joeskolengaden/marwin/Gallery/3.jpg

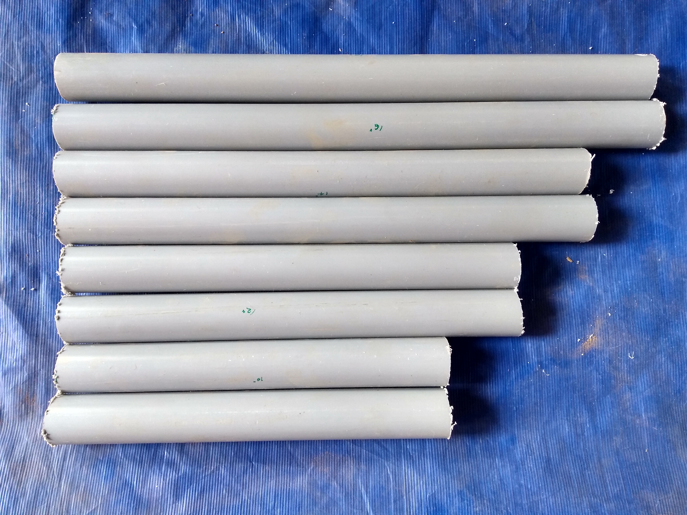
Gallery/3.jpg
