joeskolengaden/marwin/Gallery/4.jpg

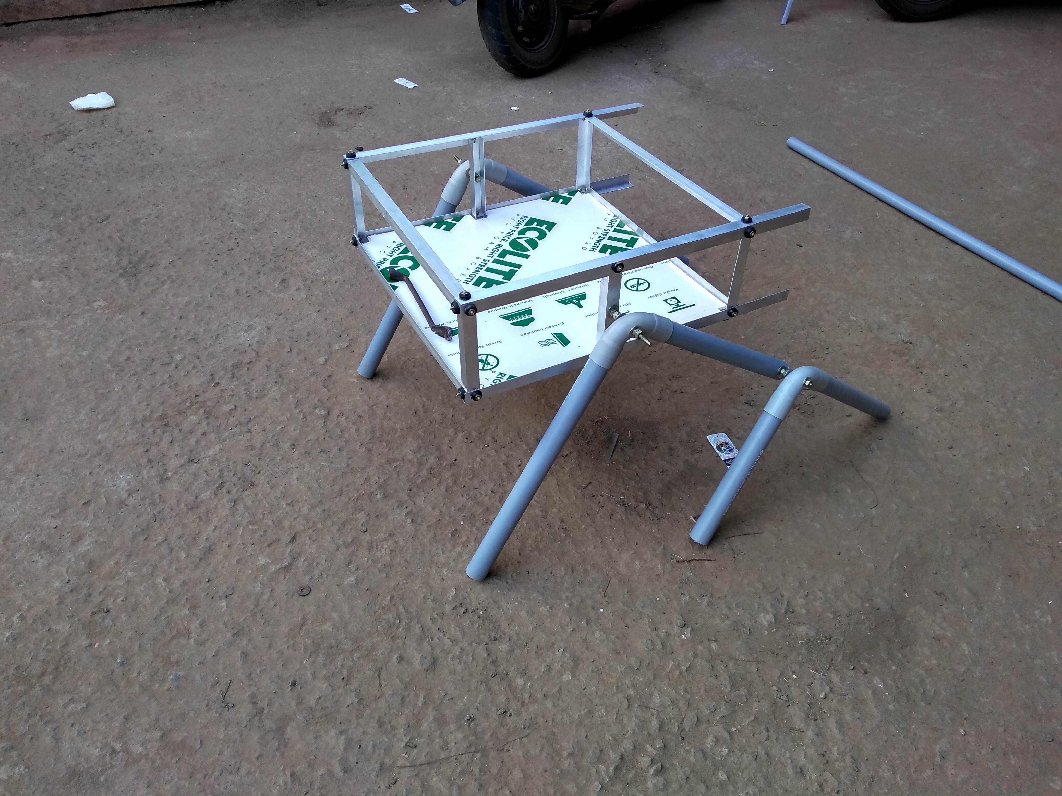
Gallery/4.jpg
