joeskolengaden/marwin/Gallery/5.jpg

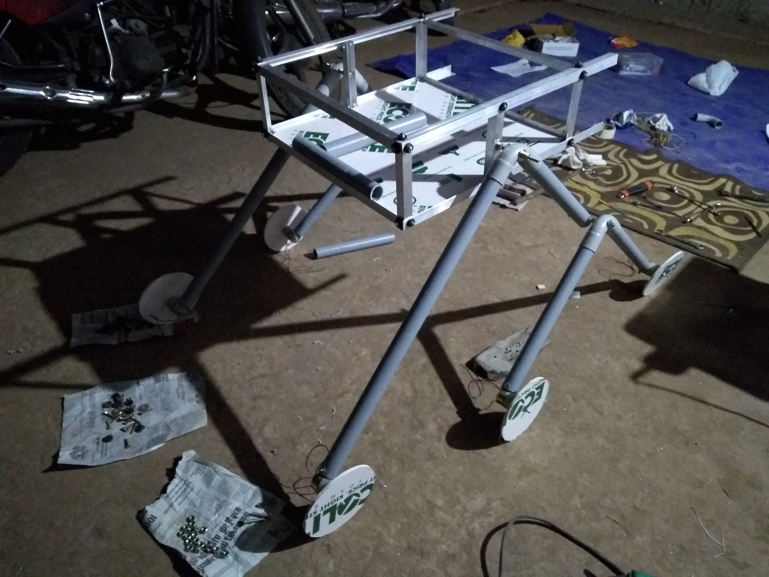
Gallery/5.jpg
