joeskolengaden/marwin/Gallery/6.jpeg

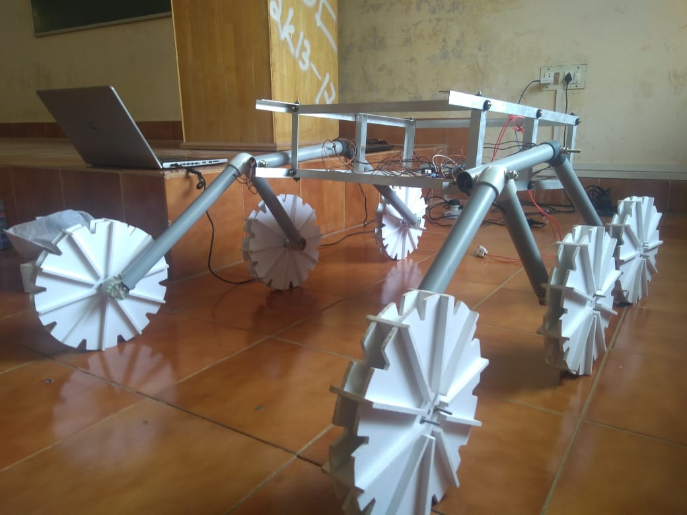
Gallery/6.jpeg
