joeskolengaden/marwin/Gallery/7.jpeg

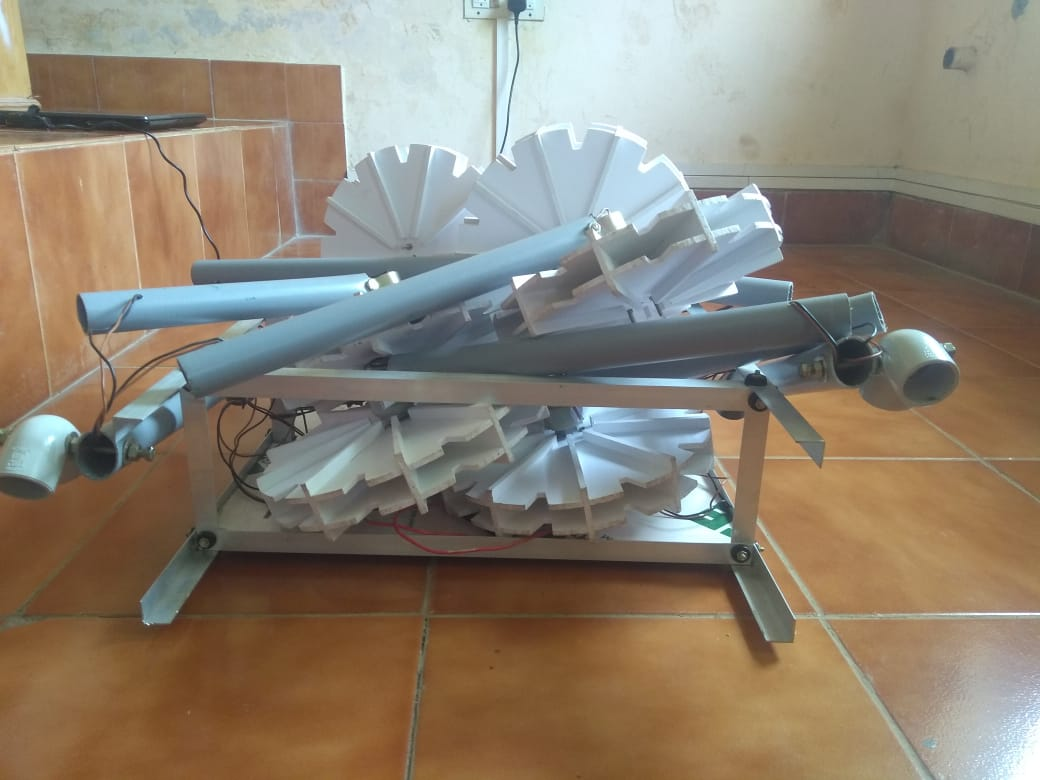
Gallery/7.jpeg
