joeskolengaden/marwin/Gallery/marwinstickerwriting.png

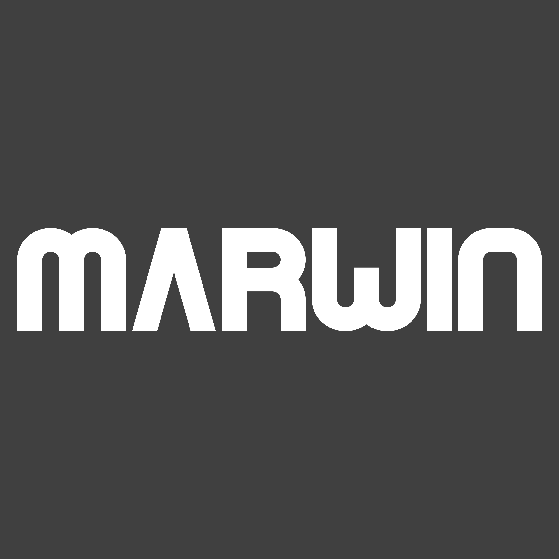
Gallery/marwinstickerwriting.png
