joeskolengaden/marwin/Gallery/sticker.jpg

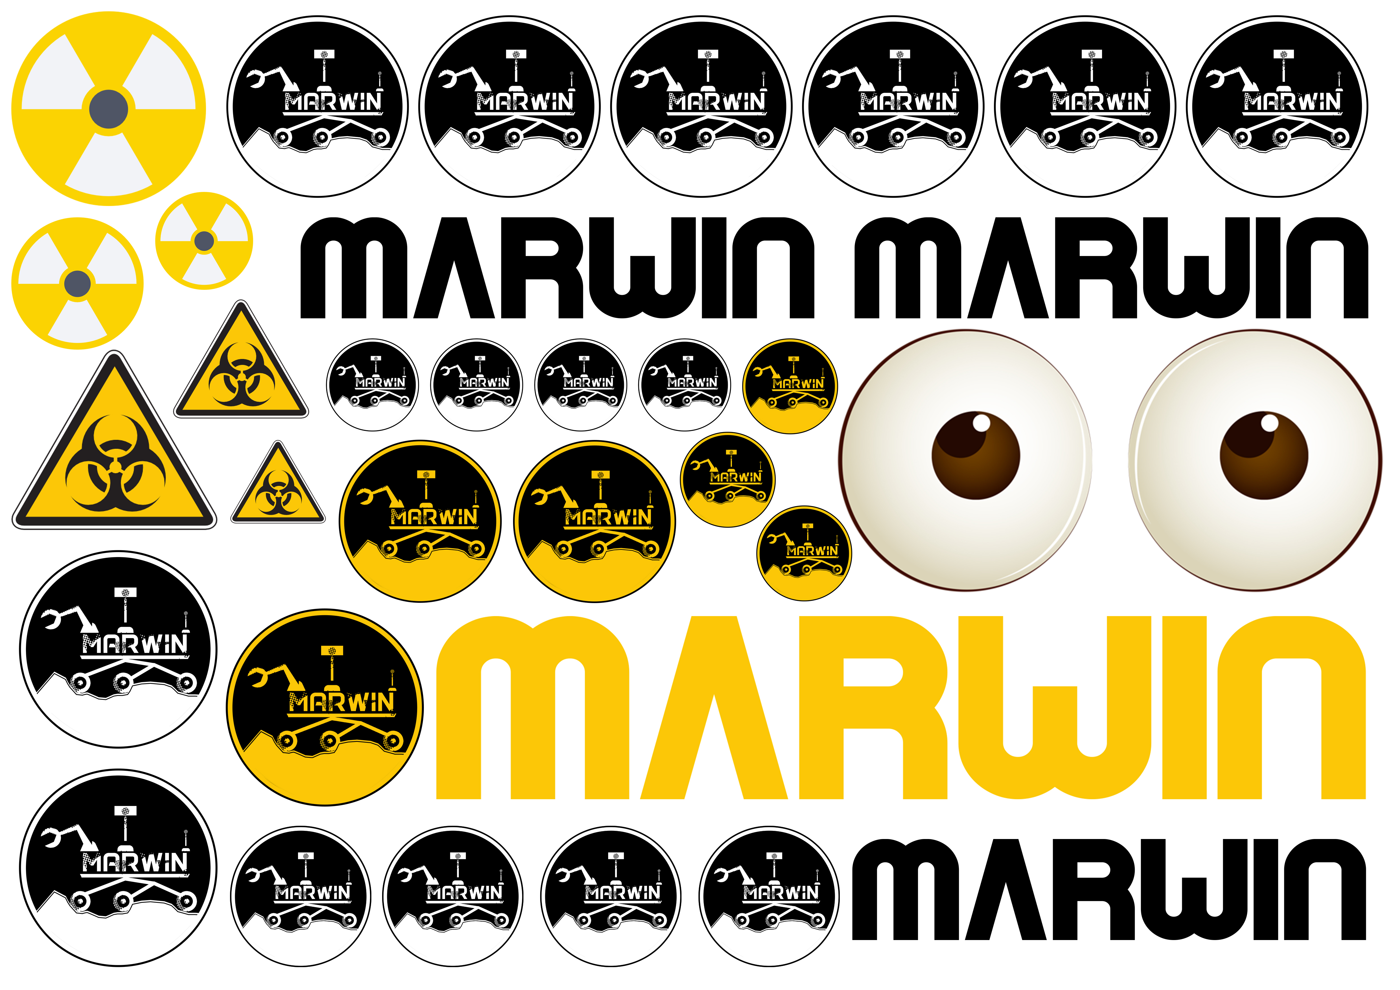
Gallery/sticker.jpg
